wodowiesel/GB-Dumper/docs/GB-Dumper-back.png

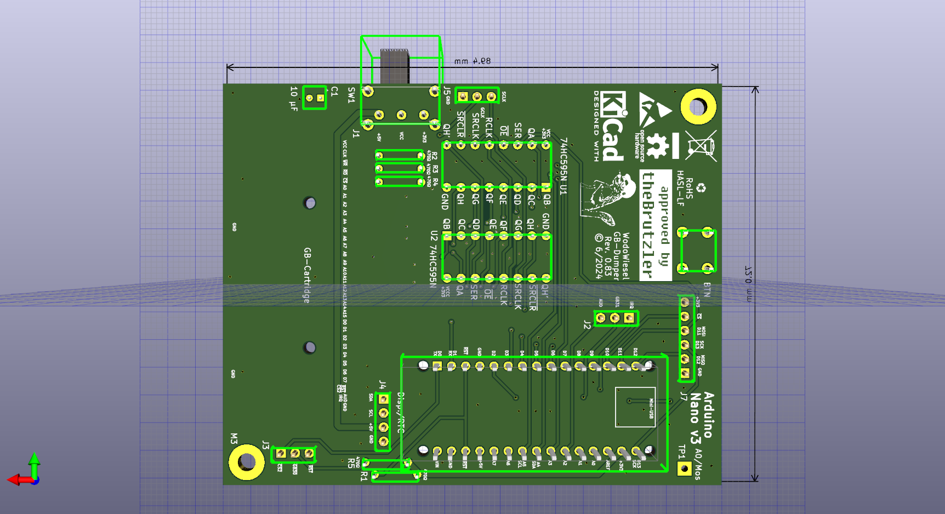
docs/GB-Dumper-back.png
