wodowiesel/GB-Dumper/docs/GB-Dumper-front.png

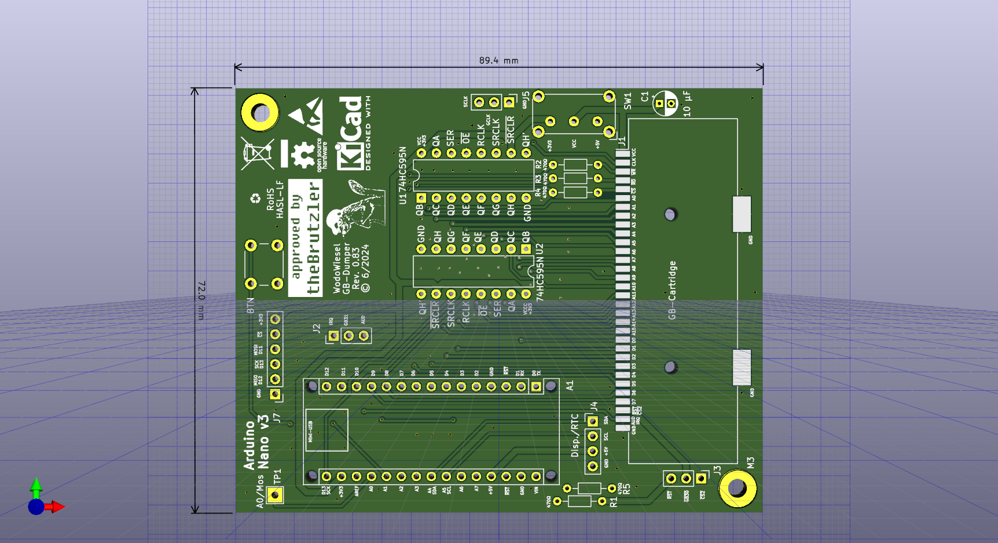
docs/GB-Dumper-front.png
