wodowiesel/GB-Dumper/docs/gb-memory-maps.png

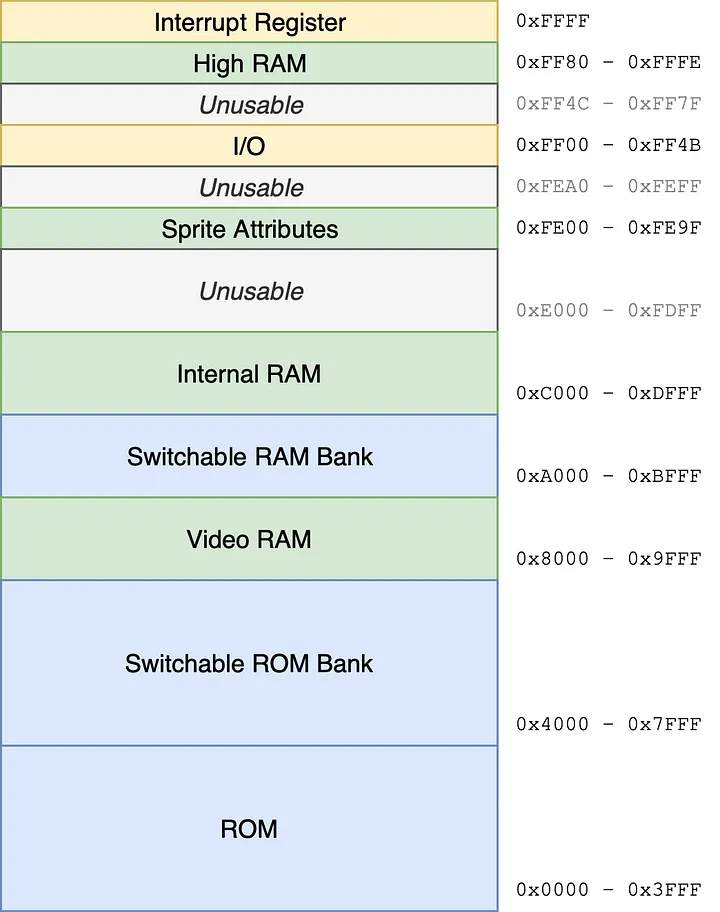
docs/gb-memory-maps.png
